DeepShift-Labs/Project-Zeta/URDF/Tuned_URDF/zeta_urdf_description/meshes/Arduino_Mount_v1_1.stl

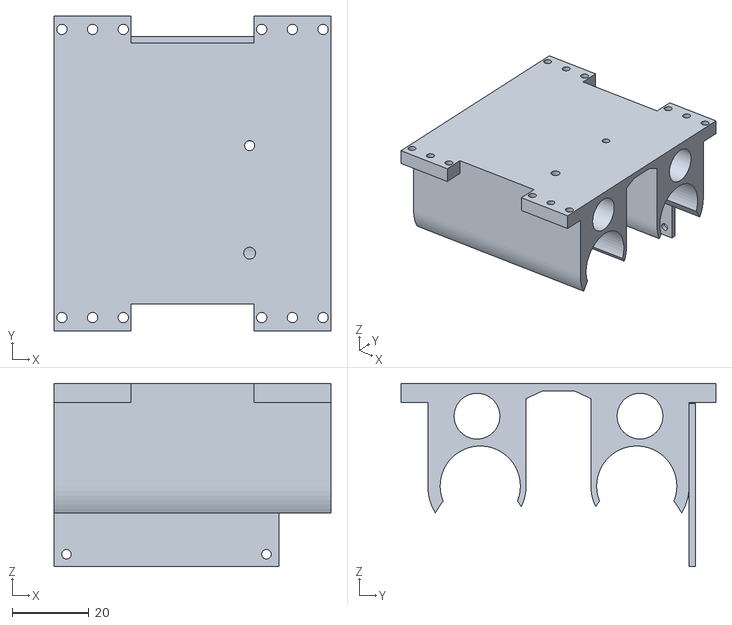
[picture p10: CAD file, 2023-02-03]
URDF/Tuned_URDF/zeta_urdf_description/meshes/Arduino_Mount_v1_1.stl
72.1 x 82.1 x 47.7
