DeepShift-Labs/Project-Zeta/ROS_Stack/src/zeta_description/meshes/base_link.stl

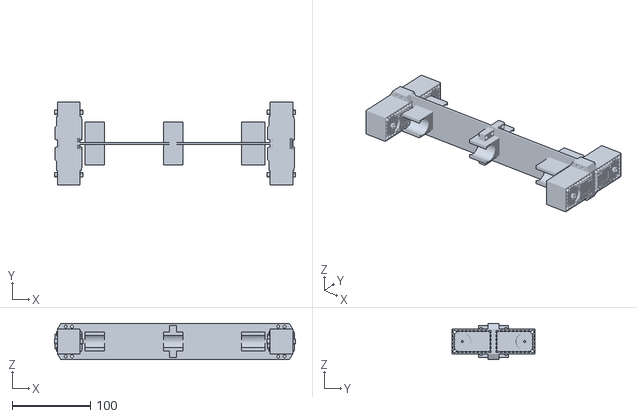
[picture p11: CAD file, 2022-02-20]
ROS_Stack/src/zeta_description/meshes/base_link.stl
307.3 x 106.4 x 46.0
