DeepShift-Labs/Project-Zeta/URDF/Tuned_URDF/zeta_urdf_description/meshes/Pi_Mount_v1_1.stl

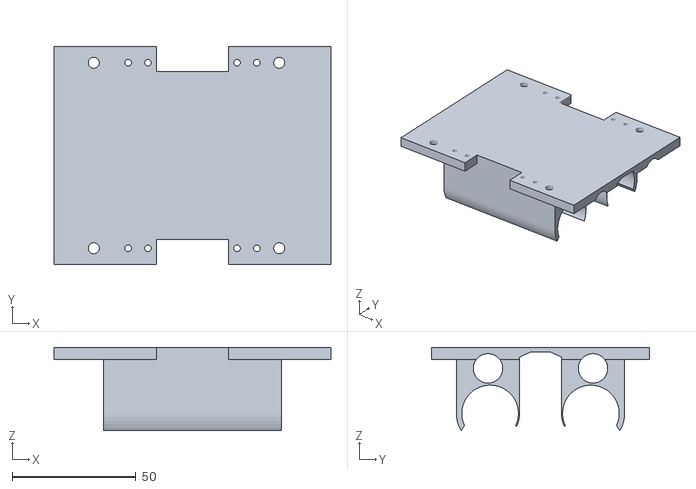
[picture p12: CAD file, 2023-02-03]
URDF/Tuned_URDF/zeta_urdf_description/meshes/Pi_Mount_v1_1.stl
112.1 x 88.1 x 33.7
