DeepShift-Labs/Project-Zeta/URDF/Tuned_URDF/zeta_urdf_description/meshes/rpi3-bottom_netfabb_v2_1.stl

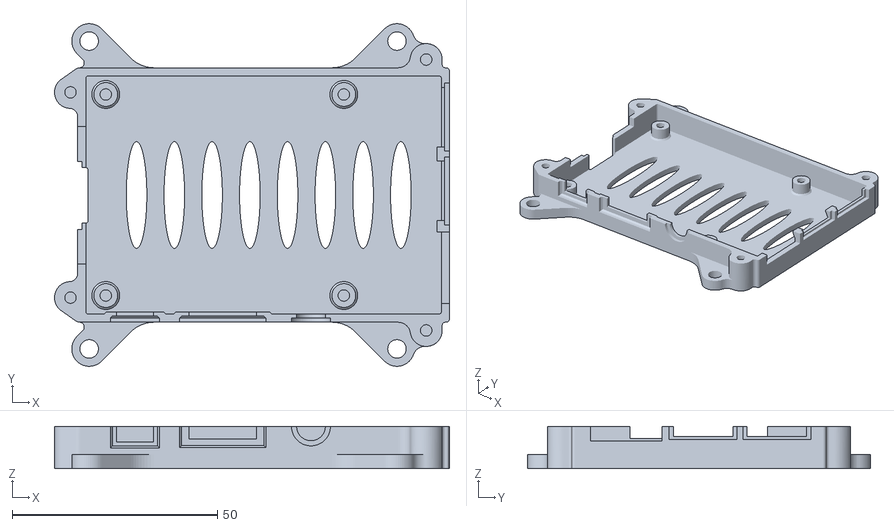
[picture p13: CAD file, 2023-02-03]
URDF/Tuned_URDF/zeta_urdf_description/meshes/rpi3-bottom_netfabb_v2_1.stl
96.2 x 83.5 x 10.3
