DeepShift-Labs/Project-Zeta/URDF/Tuned_URDF/zeta_urdf_description/meshes/ArduinoMega_STEP_AP203_v1_1.stl

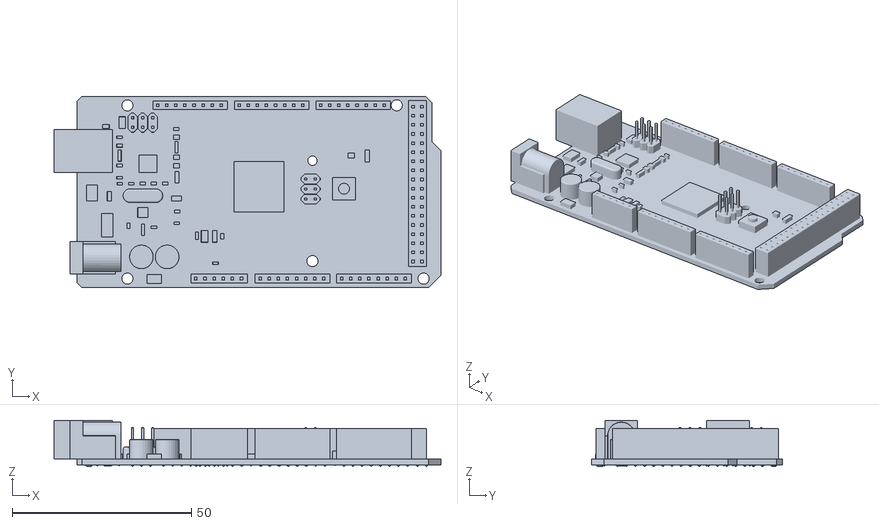
[picture p14: CAD file, 2023-02-03]
URDF/Tuned_URDF/zeta_urdf_description/meshes/ArduinoMega_STEP_AP203_v1_1.stl
108.0 x 53.4 x 13.0
