DeepShift-Labs/Project-Zeta/URDF/Tuned_URDF/zeta_urdf_description/meshes/rpi2-top_30mm-fan_netfabb_v2_1.stl

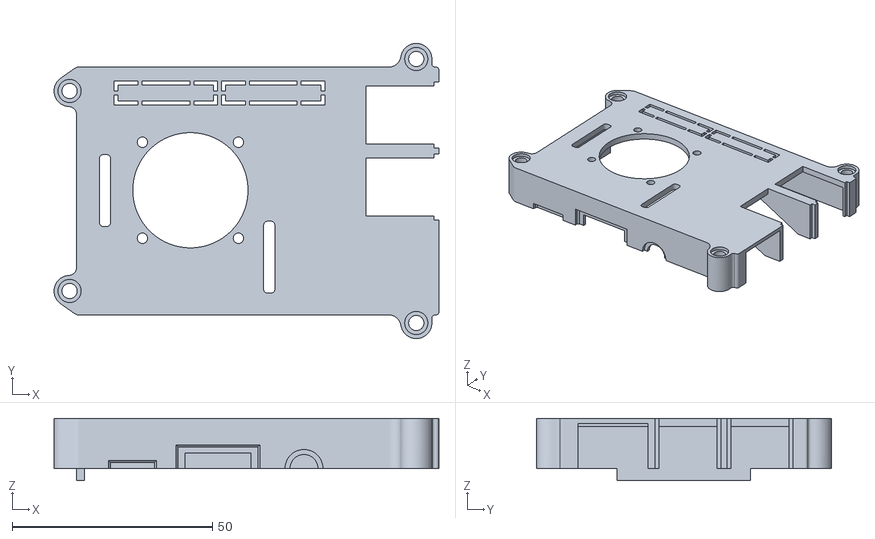
[picture p15: CAD file, 2023-02-03]
URDF/Tuned_URDF/zeta_urdf_description/meshes/rpi2-top_30mm-fan_netfabb_v2_1.stl
96.2 x 73.8 x 15.5
