DeepShift-Labs/Project-Zeta/ROS_Stack/src/Computing/inverse_kinematics_solver/src/cartesian_kinematic_server.py

#!/usr/bin/env python

from __future__ import print_function

from inverse_kinematics_solver.srv import CartesianKinematicSolver, CartesianKinematicSolverResponse
import rospy
import math

FL1 = 1
FL2 = 12
FL3 = 3
FR1 = 11
FR2 = 10
FR3 = 2
BL1 = 5
BL2 = 6
BL3 = 4
BR1 = 7
BR2 = 9
BR3 = 8

upper_leg_length = 8; #Leg length in cm for IK
lower_leg_length = 13; #Leg length in cm for IK

def map_(x, in_min, in_max, out_min, out_max):
    return (x - in_min) * (out_max - out_min) / (in_max - in_min) + out_min


def radToDeg(rad):
    return (rad * 360) / (2 * math.math.pi)


def normalize_inverse(motor_id, position):
    final_position = position
    break_val = 0
    if FL1:
        break_val = 1
    if FR1:
        break_val = 1
    if BL1:
        break_val = 1
    if BR1:
        final_position = map(position, 0, 1000, 1000, 0)
        break_val = 1
    if FL2:
        break_val = 1
    if FR2:
        break_val = 1
    if BL2:
        break_val = 1
    if BR2:
        final_position = map(position, 0, 1000, 1000, 0)
        break_val = 1
    if FL3:
        final_position = map(position, 0, 1000, 1000, 0)
        break_val = 1
    if FR3:
        final_position = final_position - 50
        break_val = 1
    if BL3:
        break_val = 1
    if BR3:
        final_position = map(position, 0, 1000, 1000, 0)
        break_val = 1
    return final_position


def degToMotorPos(motor_id, angle):
  DEGREE = 1000 / 240

  if (motor_id == FL1 or motor_id == FR1 or motor_id == BL1 or motor_id == BR1):
    if (angle > 90):
      pos = 500 + (abs(angle - 90) * DEGREE)
    
    elif (angle < 90):
      pos = 500 - (abs(angle - 90) * DEGREE)
    
    pos = round(pos)
  
  if (motor_id == FL2 or motor_id == FR2 or motor_id == BL2 or motor_id == BR2):
    if (angle > 45):
      pos = 500 - (abs(angle - 45) * DEGREE)
    elif (angle < 45):
      pos = 500 + (abs(angle - 45) * DEGREE)
    pos = round(pos)
  if (motor_id == FL3 or motor_id == FR3 or motor_id == BL3 or motor_id == BR3):
    if (angle > 90):
      pos = 500 + (abs(angle - 90) * DEGREE)
    elif (angle < 90):
      pos = 500 - (abs(angle - 90) * DEGREE)

    pos = round(pos)

  if (pos > 1000 or pos < 0):
    pos = 500

  return pos


def IK_Solver(x, y, z):
    y = y * -1
    z_alt = math.sqrt(y**2 + z**2)
    numerator_b = math.pow(z_alt, 2) - math.pow(upper_leg_length, 2) - math.pow(lower_leg_length, 2)
    denominator_b = (-2) * upper_leg_length * lower_leg_length
    theta_lower = math.acos(numerator_b / denominator_b)

    numerator_u = lower_leg_length * math.sin(theta_lower)
    theta_upper = math.asin(numerator_u / z_alt)

    mid_angle = math.atan(y / z)
    final_theta_upper = math.pi - (math.pi / 2) - theta_upper - mid_angle
    theta_joint_3 = (math.pi / 2) - math.atan(x / z)

    return theta_lower, final_theta_upper, theta_joint_3


def handle_cartesian_kinematic_solver(req):
    #print("Returning [%s, %s, %s, %s]" % (req.x, req.y, req.z, req.motor_id))
    a, b, c = IK_Solver(req.x, req.y, req.z)
    print("Returning [%s, %s, %s, %s]" % (req.x, req.y, req.z, req.motor_id))
    return CartesianKinematicSolverResponse(a, b, c)


def inverse_kinematics_server():
    rospy.init_node('cartesian_kinematic_server')
    s = rospy.Service('cartesian_kinematic_server', CartesianKinematicSolver, handle_cartesian_kinematic_solver)
    print("Ready to compute kinematics.")
    #rospy.smath.pin()
    rospy.spin()

if __name__ == "__main__":
    inverse_kinematics_server()
