DeepShift-Labs/Project-Zeta/Arduino/Project-Zeta_main/Project-Zeta_main.ino

#include <LobotServoController.h>
#include "config.h"
#include "functions.h"
//#include "serial_servo.h"



void setup() {
  if (Debug != 1) {
    pinMode(13, OUTPUT);
  }
  if (Debug != 1) {
    digitalWrite(13, LOW);
  } else if (Debug == 1) {
    digitalWrite(13, HIGH);
  }

  Serial.begin(57600);
  Serial1.begin(9600);
  Serial2.begin(115200);

  delay(1000);

  reset_motors(3000);
  home(3000);
  delay(3000);

  //low_set();

  //up stroke 1
  ik = IK(4, 0, 22);
  pos = degToPos(ik.m2, FR2);
  pos1 = degToPos(ik.m1, FR1);
  pos2 = degToPos(ik.m3, FR3);
  Controller.moveServo(FR1, pos1, time);
  Controller.moveServo(FR2, pos, time);
  Controller.moveServo(FR3, pos2, time);

  pos = degToPos(ik.m2, BL2);
  pos1 = degToPos(ik.m1, BL1);
  pos2 = degToPos(ik.m3, BL3);
  Controller.moveServo(BL1, pos1, time);
  Controller.moveServo(BL2, pos, time);
  Controller.moveServo(BL3, pos2, time);
}

void loop() {
}
