DeepShift-Labs/Project-Zeta/URDF/Raw_URDF/zeta_urdf_description_ros1/launch/controller.yaml

zeta_urdf_controller:
  # Publish all joint states -----------------------------------
  joint_state_controller:
    type: joint_state_controller/JointStateController
    publish_rate: 50

  # Position Controllers --------------------------------------
  FL_1_position_controller:
    type: effort_controllers/JointPositionController
    joint: FL_1
    pid: {p: 100.0, i: 0.01, d: 10.0}
  FL_3_position_controller:
    type: effort_controllers/JointPositionController
    joint: FL_3
    pid: {p: 100.0, i: 0.01, d: 10.0}
  FR_3_position_controller:
    type: effort_controllers/JointPositionController
    joint: FR_3
    pid: {p: 100.0, i: 0.01, d: 10.0}
  BR_3_position_controller:
    type: effort_controllers/JointPositionController
    joint: BR_3
    pid: {p: 100.0, i: 0.01, d: 10.0}
  BL_3_position_controller:
    type: effort_controllers/JointPositionController
    joint: BL_3
    pid: {p: 100.0, i: 0.01, d: 10.0}
  FL_2_position_controller:
    type: effort_controllers/JointPositionController
    joint: FL_2
    pid: {p: 100.0, i: 0.01, d: 10.0}
  BL_2_position_controller:
    type: effort_controllers/JointPositionController
    joint: BL_2
    pid: {p: 100.0, i: 0.01, d: 10.0}
  FR_1_position_controller:
    type: effort_controllers/JointPositionController
    joint: FR_1
    pid: {p: 100.0, i: 0.01, d: 10.0}
  BL_1_position_controller:
    type: effort_controllers/JointPositionController
    joint: BL_1
    pid: {p: 100.0, i: 0.01, d: 10.0}
  BR_1_position_controller:
    type: effort_controllers/JointPositionController
    joint: BR_1
    pid: {p: 100.0, i: 0.01, d: 10.0}
  FR_2_position_controller:
    type: effort_controllers/JointPositionController
    joint: FR_2
    pid: {p: 100.0, i: 0.01, d: 10.0}
  BR_2_position_controller:
    type: effort_controllers/JointPositionController
    joint: BR_2
    pid: {p: 100.0, i: 0.01, d: 10.0}
