DeepShift-Labs/Project-Zeta/Arduino/Project-Zeta_main/functions.h

//Set all motors to middle position
void reset_motors(int duration) {
  Controller.moveServos(6, duration, FL1, 500, FL2, 500, FL3, 500, FR1, 500, FR2, 500, FR3, 500); //Sets first batch of motors to 500
  delay(duration + 5); //wait for motors to finish move
  Controller.moveServos(6, duration, BL1, 500, BL2, 500, BL3, 500, BR1, 500, BR2, 500, BR3, 500); //Sets first batch of motors to 500
  delay(duration + 5); //wait for motors to finish move
  Controller.moveServos(4, duration, FL2, 500, FR2, 500, BL2, 500, BR2, 500); //Sets first batch of motors to 500
  delay(duration + 5); //wait for motors to finish move
}

//Move the motors to their normal standing position(done in to parts to ease motor load and current draw)
void home(int duration) {
  Controller.moveServos(6, duration, FL1, 500, FL2, 500, FL3, 500, FR1, 500, FR2, 500, FR3, 500);
  delay(duration / 4);
  Controller.moveServos(6, duration, BL1, 500, BL2, 500, BL3, 600, BR1, 500, BR2, 500, BR3, 500);
  delay(duration + 5);
  Controller.moveServos(4, duration, FL2, 500, FR2, 500, BL2, 500, BR2, 500);
  delay(duration + 5);
}

//Move to sitting position(done in to parts to ease motor load and current draw)
void sit(int duration) {
  Controller.moveServo(FL1, 0, duration);
  Controller.moveServo(FL2, 500, duration);
  Controller.moveServo(FL3, 500, duration);

  Controller.moveServo(BL1, 0, duration);
  Controller.moveServo(BL2, 500, duration);
  Controller.moveServo(BL3, 500, duration);

  Controller.moveServo(FR1, 1000, duration);
  Controller.moveServo(FR2, 500, duration);
  Controller.moveServo(FR3, 500, duration);

  Controller.moveServo(BR1, 1000, duration);
  Controller.moveServo(BR2, 500, duration);
  Controller.moveServo(BR3, 500, duration);
  delay(duration + 5);
}

//Convert degrees the IK provides into motor coordinates
int degToPos(int input, int motor) {
  double output;

  if (input < 90) {
    double target_angle_ = 90 - input;
    double conv_ = (target_angle_ * 1000) / 270;
    output = 500 - (conv_ * 2);
  }
  if (input > 90) {
    double target_angle_ = input - 90;
    double conv_ = (target_angle_ * 1000) / 270;
    output = (conv_ * 2) + 500;
  }
  if (input == 90) {
    output = 500;
  }

  //Invert some motors to standardize the mapping
  if (motor == BR1) {
    output = map(output, 0, 1000, 1000, 0);
  }
  if (motor == BR2) {
    output = map(output, 0, 1000, 1000, 0);
  }
  if (motor == BR3) {
    output = map(output, 0, 1000, 1000, 0);
  }
  
  if (motor == BL1) {
    output = map(output, 0, 1000, 0, 1000);
  }
  if (motor == BL2) {
    output = map(output, 0, 1000, 0, 1000);
  }
  if (motor == BL3) {
    output = map(output, 0, 1000, 1000, 0);
    output += 100;
  }

  if (motor == FR1) {
    output = map(output, 0, 1000, 1000, 0);
  }
  if (motor == FR2) {
    output = map(output, 0, 1000, 1000, 0);
  }
  if (motor == FR3) {
    output = map(output, 0, 1000, 1000, 0);
  }

  if (motor == FL1) {
    output = map(output, 0, 1000, 0, 1000);
  }
  if (motor == FL2) {
    output = map(output, 0, 1000, 0, 1000);
  }
  if (motor == FL3) {
    output = map(output, 0, 1000, 1000, 0);
  }
  return int(round(output));
}

//Convert degrees to radians
double radToDeg(double rad) {
  double deg = rad * 180;
  deg = deg / PI;
  return deg;
}

//Work around to C's restriction of functions returning an array. You can create a custom structure and set that as the function type.
struct IK_out {
  double m1, m2, m3;
};

//The main IK function. This is complex to explain so I will have a video explaining it. 
IK_out IK(float x, float y, float z) {

  //Up-Down Motion
  z = z - 5;
  double divisor = pow(z, 2) - pow(upper_leg_length, 2) - pow(lower_leg_length, 2);
  divisor = divisor * -1;
  double dividend = 2 * upper_leg_length * lower_leg_length;
  double quotient = divisor / dividend;
  double theta_z = acos(quotient);

  theta_z = radToDeg(theta_z);

  //Forward-Backward Motion
  x = x * -1;
  double theta_t = atan((x/z)); //cos but doesn't work
  theta_t = radToDeg(theta_t);
  double theta_x = 90 - theta_t;

  //Rotate Translate Axis
  double theta_y = asin(y/z);
  theta_y = radToDeg(theta_y);
  theta_y = 90 - theta_y;

  return {theta_z, theta_x, theta_y};
}

//Useless garbage that you don't need to worry about.
IK_out ik, ik2;
int pos, pos1, pos2;

void low_set() {
  ik = IK(0, 0, 26);
  pos = degToPos(ik.m2, FR2);
  pos1 = degToPos(ik.m1, FR1);
  pos2 = degToPos(ik.m3, FR3);
  Controller.moveServo(FR2, pos, time);
  Controller.moveServo(FR1, pos1, time);
  Controller.moveServo(FR3, pos2, time);

  pos = degToPos(ik.m2, BR2);
  pos1 = degToPos(ik.m1, BR1);
  pos2 = degToPos(ik.m3, BR3);
  Controller.moveServo(BR2, pos, time);
  Controller.moveServo(BR1, pos1, time);
  Controller.moveServo(BR3, pos2, time);

  pos = degToPos(ik.m2, BL2);
  pos1 = degToPos(ik.m1, BL1);
  pos2 = degToPos(ik.m3, BL3);
  Controller.moveServo(BL2, pos, time);
  Controller.moveServo(BL1, pos1, time);
  Controller.moveServo(BL3, pos2, time);

  pos = degToPos(ik.m2, FL2);
  pos1 = degToPos(ik.m1, FL1);
  pos2 = degToPos(ik.m3, FL3);
  Controller.moveServo(FL2, pos, time);
  Controller.moveServo(FL1, pos1, time);
  Controller.moveServo(FL3, pos2, time);
  delay(time);
}
